m-marini/wheellino/WheellyESP32/ApiServer.cpp

/*
 * Copyright (c) 2023  Marco Marini, marco.marini@mmarini.org
 *
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
 *    END OF TERMS AND CONDITIONS
 *
 */

#include <ESPmDNS.h>
#include <ArduinoJson.h>
#include <esp_system.h>
#include <WiFi.h>

#include "ApiServer.h"
#include "ConfStore.h"

#include <esp_log.h>
static const char *TAG = "ApiServer";

#define HTTP_METHOD_GET ((HTTPMethod)1)
#define HTTP_METHOD_POST ((HTTPMethod)3)
#define RESTART_DELAY 500

static const char *DEFAULT_SERVER_NAME = "wheelly";
static const unsigned long MAX_SCAN_DURATION = 1000000;

ApiServerClass ApiServer;

/*
  Send error
*/
void sendError(const int httpCode, const String &msg) {
  StaticJsonDocument<256> jsonDoc;
  String response;
  jsonDoc["message"] = msg;
  serializeJson(jsonDoc, response);
  ApiServer._server.send(httpCode, "application/json", response);
  ApiServer.setActivity();
}

static const String methodName(const HTTPMethod method) {
  String result("Unknown");
  switch (method) {
    case HTTP_METHOD_GET:
      result = "GET";
      break;
  }
  return result;
}

/*
  Handles not found page
*/
void handleNotFound(void) {
  ESP_LOGD(TAG, "handleNotFound method %d", (int)ApiServer._server.method());
  StaticJsonDocument<256> jsonDoc;
  jsonDoc.clear();
  jsonDoc["message"] = "Not Found";
  jsonDoc["url"] = ApiServer._server.uri();
  jsonDoc["method"] = methodName(ApiServer._server.method());
  String response;
  serializeJson(jsonDoc, response);
  ESP_LOGE(TAG, "404 - %s", response.c_str());
  ApiServer._server.send(404, "application/json", response);
  ApiServer.setActivity();
}

/*
   Handles netwok list request
*/
void handleGetNetworkList(void) {
  ESP_LOGD(TAG, "Scanning networks...");
  ApiServer.setActivity();
  StaticJsonDocument<256> jsonDoc;
  JsonArray data = jsonDoc.createNestedArray("networks");
  int scanResult = WiFi.scanNetworks(false, true);
  for (int i = 0; i < scanResult; i++) {
    data.add(WiFi.SSID(i));
  }
  String response;
  serializeJson(jsonDoc, response);
  ApiServer._server.send(200, "application/json", response);
}

/*
   Handles the configuration request
*/
void handleGetConfig(void) {
  ESP_LOGD(TAG, "handleGetWiFiConfig");
  StaticJsonDocument<256> jsonDoc;
  ConfStore::toJson(jsonDoc, ApiServer._confStore->config());

  String response;
  serializeJson(jsonDoc, response);
  ApiServer._server.send(200, "application/json", response);
  ApiServer.setActivity();
}

/*
   Handles the configuration request
*/
void handleGetWheellyId(void) {
  ESP_LOGD(TAG, "handleGetWheellyId");
  JsonDocument jsonDoc;
  jsonDoc["id"] = ApiServer._wheellyId;

  String response;
  serializeJson(jsonDoc, response);
  ApiServer._server.send(200, "application/json", response);
  ApiServer.setActivity();
}

/*
   Handles the wifi configuration request
*/
void handlePostConfig(void) {
  ESP_LOGD(TAG, "handlePostWiFiConfig");
  // Retrive body
  String body = ApiServer._server.arg("plain");
  ESP_LOGD(TAG, "Body=%s", body.c_str());
  JsonDocument jsonDoc;
  if (deserializeJson(jsonDoc, body) != DeserializationError::Ok) {
    sendError(400, "Malformed JSON");
    return;
  }
  ConfigRecord config;
  const ConfStoreRetCode rc = ConfStore::fromJson(config, jsonDoc);
  if (rc != SUCCESS) {
    String text = String("Bad configuration RC=") + rc;
    sendError(400, text);
    return;
  }

  String response;
  serializeJson(jsonDoc, response);

  const ConfStoreRetCode rc1 = ApiServer._confStore->store(config);
  if (rc1 != SUCCESS) {
    String text = String("Bad configuration RC=") + rc1;
    sendError(400, text);
    return;
  }

  ESP_LOGI(TAG, "WiFi configuration: %s", response.c_str());
  ApiServer._server.send(200, "application/json", response);
  ApiServer.setActivity();
}

/*
   Handles the wifi configuration request
*/
void handlePostRestart(void) {
  ESP_LOGD(TAG, "handleRestart");
  StaticJsonDocument<256> jsonDoc;
  jsonDoc.clear();
  jsonDoc["restart"] = true;

  String response;
  serializeJson(jsonDoc, response);
  ApiServer._server.send(200, "application/json", response);
  ApiServer.setActivity();
  ApiServer._restartInstant = millis() + RESTART_DELAY;
}

void ApiServerClass::begin(const String &wheellyId, ConfStore &confStore) {
  ESP_LOGI(TAG, "Begin");
  _confStore = &confStore;
  _wheellyId = wheellyId;
}

void ApiServerClass::start(void) {
  ESP_LOGD(TAG, "Starting api server ...");

  if (!MDNS.begin(DEFAULT_SERVER_NAME)) {
    ESP_LOGD(TAG, "Error starting dns responder.");
  } else {
    ESP_LOGI(TAG, "Started MDNS");
  }
  ESP_LOGD(TAG, "_apiServer.begin()");
  _server.begin();
  ESP_LOGD(TAG, "_apiServer configuration");
  _server.on("/api/v2/wheelly/restart", HTTP_METHOD_POST, handlePostRestart);
  _server.on("/api/v2/wheelly/config", HTTP_METHOD_GET, handleGetConfig);
  _server.on("/api/v2/wheelly/config", HTTP_METHOD_POST, handlePostConfig);
  _server.on("/api/v2/wheelly/networks", HTTP_METHOD_GET, handleGetNetworkList);
  _server.on("/api/v2/wheelly/id", HTTP_METHOD_GET, handleGetWheellyId);
  _server.onNotFound(handleNotFound);
  ESP_LOGD(TAG, "Started api server.");
}

void ApiServerClass::polling(const unsigned long t0) {
  _server.handleClient();
  if (_restartInstant > 0 && t0 > _restartInstant) {
    esp_restart();
  }
}
