m-marini/wheellino/tests/MPUTest/MPUTest.ino

/*
 * Copyright (c) 2023  Marco Marini, marco.marini@mmarini.org
 *
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
 *    END OF TERMS AND CONDITIONS
 *
 */

#include "Arduino.h"
#include <Wire.h>

#include <esp_log.h>
static char* TAG = "MPUTest";

#include "mpu6050mm.h"
#include "num.h"

#define SERIAL_BPS 115200
#define WIRE_CLOCK 400000

#define GYRO_TEST_DURATION_MS 5000

#define EXPECTED_FREQUENCE 125.0
#define FREQUENCE_THRESHOLD 10.0
#define MAX_SAMPLES_COUNT 1024
#define GYRO_THRESHOLD 4.0
#define ACC_THRESHOLD_G 0.1
#define YAW_THRESHOLD_DEG (1.0 / 10000 * GYRO_TEST_DURATION_MS)
#define SIGMA_THRESHOLD_DEG 0.5

#define READ_ACC_TIMEOUT_US 10000
#define READ_FIFO_TIMEOUT_US 10000

static int sampleCounter;
static float yawData[MAX_SAMPLES_COUNT];

MPU6050Class Mpu;

void setup() {
  Serial.begin(SERIAL_BPS);
  while (!Serial) {
    delay(10);
  }
  Wire.begin();
  Wire.setClock(WIRE_CLOCK);
  Wire.setTimeOut(50);
  int n = 0;
  int err = 0;
  if (!testRead(++n, "WHO_AM_I_REG", WHO_AM_I_REG, 0x68)) {
    err++;
  }
  if (!testWriteRead(++n, "PWR_MGMT_1_REG", PWR_MGMT_1_REG, CLKSEL_Z_AXIS, CLKSEL_Z_AXIS)) {
    err++;
  }
  if (!testWriteRead(++n, "SMPRT_DIV_REG", SMPRT_DIV_REG, 7, 7)) {
    err++;
  }
  if (!testWriteRead(++n, "CONFIG_REG", CONFIG_REG, DLPF_1, DLPF_1)) {
    err++;
  }
  if (!testWriteRead(++n, "GYRO_CONFIG_REG", GYRO_CONFIG_REG,
                     FS_2000 << 3, FS_2000 << 3)) {
    err++;
  }
  if (!testWriteRead(++n, "ACCEL_CONFIG_REG", ACCEL_CONFIG_REG,
                     AFS_16G << 3, AFS_16G << 3)) {
    err++;
  }
  if (!testWriteRead(++n, "FIFO_EN_REG",
                     FIFO_EN_REG, XG_FIFO_EN | YG_FIFO_EN | ZG_FIFO_EN,
                     XG_FIFO_EN | YG_FIFO_EN | ZG_FIFO_EN)) {
    err++;
  }
  if (!testWriteRead(++n, "INT_PIN_CFG_REG", INT_PIN_CFG_REG,
                     INT_LEVEL | LATCH_INT_EN | INT_RD_CLEAR,
                     INT_LEVEL | LATCH_INT_EN | INT_RD_CLEAR)) {
    err++;
  }
  if (!testWriteRead(++n, "INT_ENABLE_REG", INT_ENABLE_REG,
                     FIFO_OFLOW_EN | I2C_MST_EN | DATA_RDY_EN,
                     FIFO_OFLOW_EN | I2C_MST_EN | DATA_RDY_EN)) {
    err++;
  }
  if (!testWriteRead(++n, "USER_CTRL_REG", USER_CTRL_REG, FIFO_EN_UC, FIFO_EN_UC)) {
    err++;
  }

  if (!testReadAcc(++n)) {
    err++;
  }

  if (!testGyroBuffer(++n)) {
    err++;
  }

  if (!testCalibration(++n)) {
    err++;
  }
  if (!testGyro(++n)) {
    err++;
  }
  ESP_LOGI(TAG, "Failed %d, success %d, total %d", err, n - err, n);
}

void loop() {
  delay(10000);
}

static const boolean testGyroBuffer(const int n) {
  char name[128];
  sprintf(name, "Test gyroscope buffer");
  ESP_LOGI(TAG, "%d. %s", n, name);

  uint8_t rc = Mpu.reset();
  if (rc != 0) {
    printRc("KO reset", rc);
    return false;
  }
  rc = Mpu.begin();
  if (rc != 0) {
    printRc("KO begin", rc);
    return false;
  }

  const unsigned long t0 = millis();
  const unsigned long timeout = t0 + GYRO_TEST_DURATION_MS;
  unsigned long t1;
  sampleCounter = 0;
  Vector3 gyroAverage;
  do {
    t1 = millis();
    rc = Mpu.rc();
    if (rc) {
      break;
    }
    Vector3 gyro;
    if (Mpu.getGyro(gyro)) {
      gyroAverage += gyro;
      sampleCounter++;
    }
  } while (t1 < timeout);

  if (rc != 0) {
    printRc("KO reading buffer", rc);
    return false;
  }

  if (sampleCounter <= 0) {
    ESP_LOGE(TAG, "KO %s no data read", name);
    return false;
  }

  float freq = 1000.0 * sampleCounter / (t1 - t0);
  if (abs(freq - EXPECTED_FREQUENCE) > FREQUENCE_THRESHOLD) {
    ESP_LOGE(TAG, "KO %s unexpected frequence: %.2f, expected: %f", name, (double)freq, EXPECTED_FREQUENCE);
    return false;
  }

  gyroAverage /= sampleCounter;
  ESP_LOGI(TAG, "OK %s, sample counter: %d, frequency: %.2f, gyroAverage: %s", name, sampleCounter, (double)freq, gyroAverage.toString().c_str());
  return true;
}

static const boolean testGyro(const int n) {
  char name[128];
  sprintf(name, "Test gyroscope");
  ESP_LOGI(TAG, "%d. %s", n, name);

  uint8_t rc = Mpu.reset();
  if (rc != 0) {
    printRc("KO reset", rc);
    return false;
  }
  rc = Mpu.begin();
  if (rc != 0) {
    printRc("KO begin", rc);
    return false;
  }
  rc = Mpu.calibrate();
  if (rc != 0) {
    printRc("KO calibration", rc);
    return false;
  }

  const unsigned long t0 = millis();
  const unsigned long timeout = t0 + GYRO_TEST_DURATION_MS;
  unsigned long t1;

  // Accumulates data on buffer
  sampleCounter = 0;
  Mpu.onData([](void* ctx) {
    yawData[sampleCounter++] = Mpu.yaw();
  });
  do {
    t1 = millis();
    Mpu.polling(t1);
    rc = Mpu.rc();
    if (rc) {
      break;
    }
  } while (t1 < timeout && sampleCounter < MAX_SAMPLES_COUNT);

  if (rc != 0) {
    printRc("KO polling", rc);
    return false;
  }

  if (sampleCounter == 0) {
    ESP_LOGE(TAG, "KO no samples");
    return false;
  }

  float freq = 1000.0 * sampleCounter / (t1 - t0);
  if (abs(freq - EXPECTED_FREQUENCE) > FREQUENCE_THRESHOLD) {
    ESP_LOGE(TAG, "KO %s unexpected frequence: %.2f, expected: %f, sample counter: %d", name, freq, EXPECTED_FREQUENCE, sampleCounter);
    return false;
  }

  // Computes average yaw
  float avgYaw = 0;
  for (int i = 0; i < sampleCounter; i++) {
    avgYaw += yawData[i];
  }
  avgYaw /= sampleCounter;

  // Computes sigma
  float sigma = 0;
  for (int i = 0; i < sampleCounter; i++) {
    float diff = normalRad(yawData[i] - avgYaw);
    sigma += diff * diff;
  }
  sigma = sqrt(sigma / (sampleCounter - 1));

  if (abs(avgYaw * 180 / PI) > YAW_THRESHOLD_DEG) {
    ESP_LOGE(TAG, "KO %s unexpected yaw (>%.4f), sample counter: %d, yaw: %.4f, sigma: %.4f",
             name, YAW_THRESHOLD_DEG, sampleCounter, avgYaw * 180 / PI, sigma * 180 / PI);
    return false;
  }

  if (sigma * 180 / PI > SIGMA_THRESHOLD_DEG) {
    ESP_LOGE(TAG, "KO %s unexpected sigma (>%.4f), sample counter: %d, yaw: %.4f, sigma: %.4f",
             name, SIGMA_THRESHOLD_DEG, sampleCounter, avgYaw * 180 / PI, sigma * 180 / PI);
    return false;
  }

  ESP_LOGI(TAG, "OK %s, sample counter: %d, yaw: %.4f, sigma: %.4f",
           name, sampleCounter, avgYaw * 180 / PI, sigma * 180 / PI);
  return true;
}

static const boolean testCalibration(const int n) {
  char name[128];
  sprintf(name, "Test calibration");
  ESP_LOGI(TAG, "%d. %s", n, name);

  uint8_t rc = Mpu.reset();
  if (rc != 0) {
    printRc("KO reset", rc);
    return false;
  }
  rc = Mpu.begin();
  if (rc != 0) {
    printRc("KO begin", rc);
    return false;
  }
  rc = Mpu.calibrate();
  if (rc != 0) {
    printRc("KO calibration", rc);
    return false;
  }

  const Vector3& grav = Mpu.gravity();

  if (abs(grav[0]) > ACC_THRESHOLD_G
      || abs(grav[1]) > ACC_THRESHOLD_G
      || abs(grav[2]) < 1 - ACC_THRESHOLD_G
      || abs(grav[2]) > 1 + ACC_THRESHOLD_G) {
    ESP_LOGE(TAG, "KO gravity out of range, %s", grav.toString().c_str());
    return false;
  }

  const Vector3& gyroOffset = Mpu.gyroOffset();
  if (abs(gyroOffset[0]) > GYRO_THRESHOLD
      || abs(gyroOffset[1]) > GYRO_THRESHOLD
      || abs(gyroOffset[2]) > GYRO_THRESHOLD) {
    ESP_LOGE(TAG, "KO gyroOffset out of range, %s", gyroOffset.toString().c_str());
    return false;
  }

  ESP_LOGI(TAG, "OK %s gravity: %s, offset: %s",
           name, grav.toString().c_str(), gyroOffset.toString().c_str());
  return true;
}

static const boolean testReadAcc(const int n) {
  char name[128];
  sprintf(name, "Test mpu read acceleration");
  // Write divider
  ESP_LOGI(TAG, "%d. %s", n, name);

  uint8_t rc = Mpu.reset();
  if (rc != 0) {
    printRc("KO reset", rc);
    return false;
  }

  rc = Mpu.begin();
  if (rc != 0) {
    printRc("KO begin", rc);
    return false;
  }

  // Wait for data ready
  unsigned long t0 = micros();
  unsigned long timout = t0 + READ_ACC_TIMEOUT_US;
  unsigned long t1;
  do {
    rc = Mpu.readIntStatus();
    if (rc != 0) {
      printRc("KO readStatus", rc);
      return false;
    }
    t1 = micros();
  } while (!Mpu.dataReady() && t1 <= timout);

  if (!Mpu.dataReady()) {
    printRc("KO data ready timed out", rc);
    return false;
  }

  Vector3 acc;
  rc = Mpu.readAcc(acc);
  if (rc != 0) {
    printRc("KO readAcc", rc);
    return false;
  }

  ESP_LOGI(TAG, "OK %s, %s in %lu us",
           name, acc.toString().c_str(), t1 - t0);
  return true;
}

static const boolean testWriteRead(const int n, const char* regName, const uint8_t reg, const uint8_t value, const uint8_t expected) {
  return testWrite(n, regName, reg, value)
         && testRead(n, regName, reg, expected);
}

static const boolean testRead(const int n, const char* regName, const uint8_t reg, const uint8_t expected) {
  char name[128];
  sprintf(name, "Test mpu read registry %s (0x%hx)", regName, reg);
  // Write divider
  ESP_LOGI(TAG, "%d. %s", n, name);
  uint8_t bfr;
  uint8_t rc = Mpu.mpuRegRead(reg, &bfr, 1);
  if (rc != 0) {
    printRc("KO", rc);
    return false;
  }
  if (bfr != expected) {
    ESP_LOGE(TAG, "KO wrong value 0x%hhx, expected 0x%hhx", bfr, expected);
    return false;
  }
  ESP_LOGI(TAG, "OK %s", name);
  return true;
}


static const boolean testWrite(const int n, const char* regName, const uint8_t reg, const uint8_t value) {
  char name[128];
  sprintf(name, "Test mpu write registry %s (0x%hx) value 0x%hx", regName, reg, value);
  // Write divider
  ESP_LOGI(TAG, "%d. %s", n, name);
  uint8_t rc = Mpu.mpuRegWrite(reg, value);
  if (rc != 0) {
    printRc("KO", rc);
    return false;
  }
  ESP_LOGI(TAG, "OK %s", name);
  return true;
}

static void printRc(const char* str, const uint8_t rc) {
  char* descr = "???";
  switch (rc) {
    case 0:
      descr = "OK";
      break;
    case 1:
      descr = "data too long to fit in transmit buffer";
      break;
    case 2:
      descr = "received NACK on transmit of address";
      break;
    case 3:
      descr = "received NACK on transmit of data";
      break;
    case 4:
      descr = "other error";
      break;
    case 5:
      descr = "timeout";
      break;
    case READ_LEN_ERROR:
      descr = "read length error";
      break;
  }
  ESP_LOGE(TAG, "%s rc=%hhu %s", str, rc, descr);
}

void sendReply(const char* data) {}
